spirledaxis/LNMQ-Alarm-Clock/main/IMG_9301.JPEG

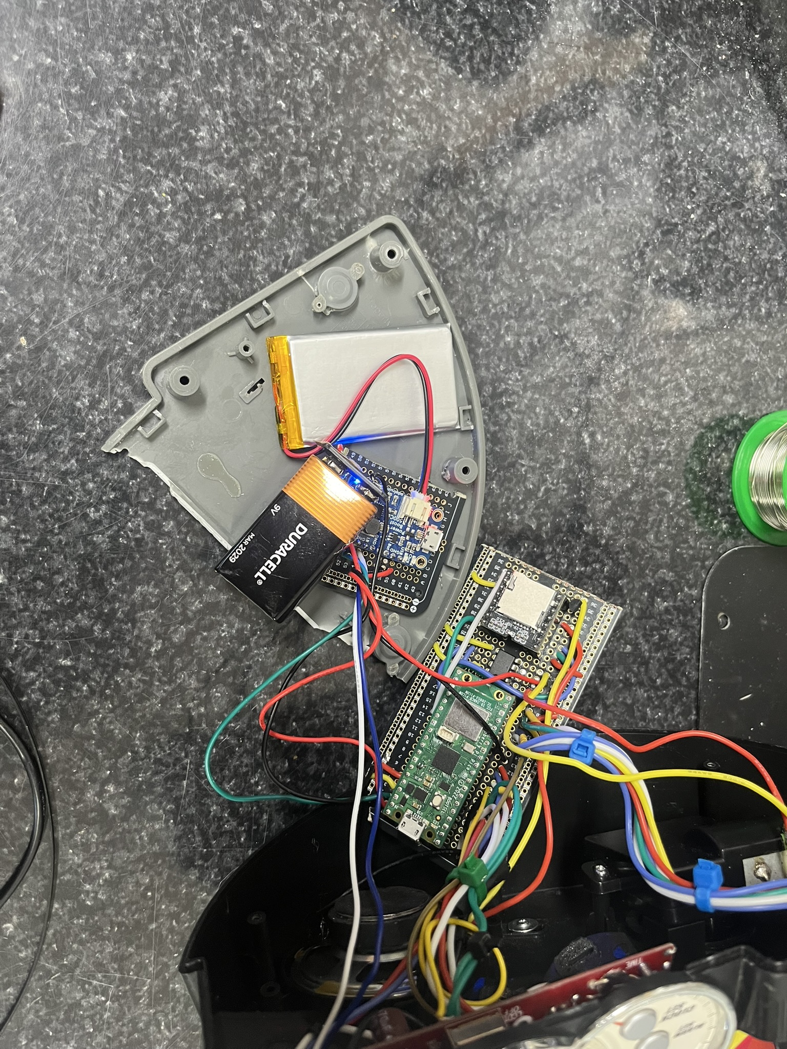
main/IMG_9301.JPEG
