spirledaxis/LNMQ-Alarm-Clock/main/IMG_9304.JPEG

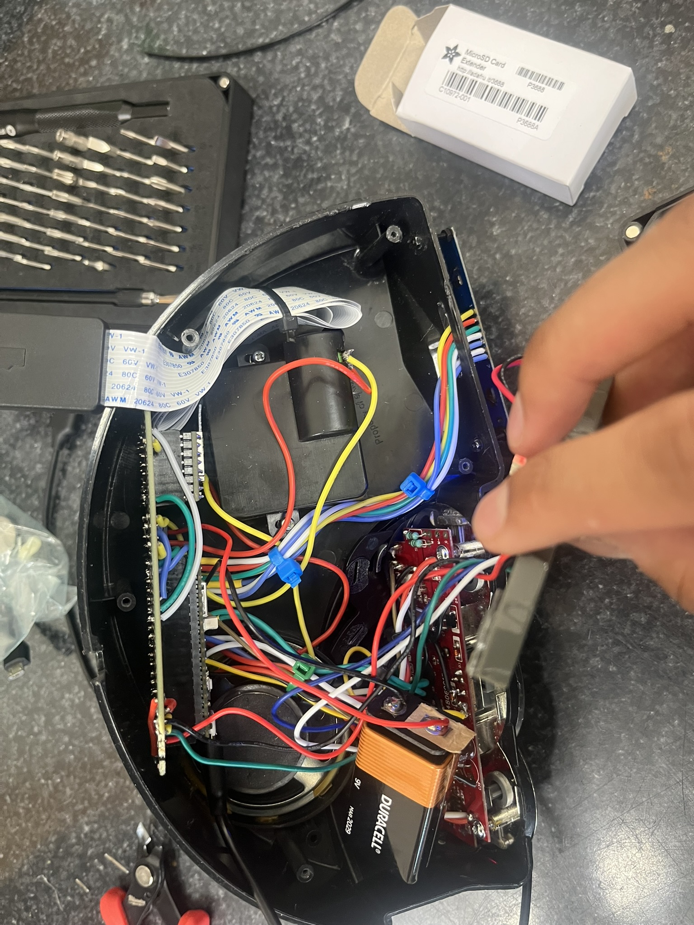
main/IMG_9304.JPEG
