spirledaxis/LNMQ-Alarm-Clock/main/IMG_9452.jpg

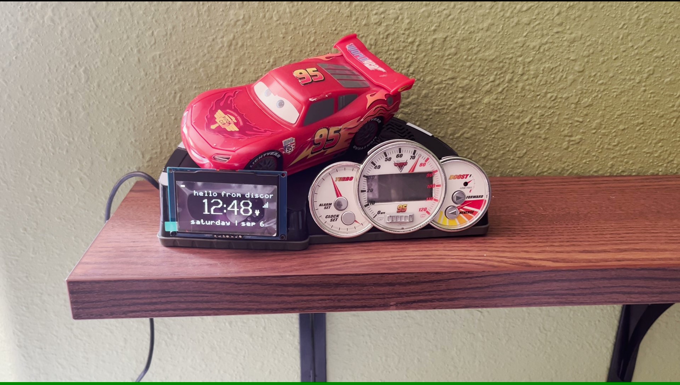
main/IMG_9452.jpg
