spirledaxis/LNMQ-Alarm-Clock/hardware/motor_movements.py

i_am_speed = [
    ('w', 600, 100),
    ('r', 1133, 30),  # exhale
    ('l', 733, 40),  # exhale 2
    ('w', 6300, 100),
    ('r', 2184, 100),  # racing sounds
    ('l', 1133, 80),  # one winner
    ('r', 1183, 80),  # 42 losers
    ('w', 2634, 100),  # I eat losers for breakfeast
    ('r', 2633, 100),  # racing sounds
    ('w', 813, 100),  # "speed"
    ('r', 2500, 100),  # racing sounds
    ('l', 884, 80),  # I am faster than fast
    ('r', 1150, 80),  # quicker than quick
    ('w', 1433, 100),  # I am lightning
]

freedom_dive = [
    ('l', 333.0, 100),
    ('r', 833.0, 100),
    ('l', 867.0, 100),
    ('r', 1017.0, 100),
    ('l', 1100.0, 100),
    ('r', 1100.0, 100),
    ('l', 1050.0, 100),
    ('r', 1066.0, 100),
    ('l', 567.0, 100),
    ('r', 567.0, 100),
    ('l', 1250.0, 100),
    ('r', 1066.0, 100),
    ('l', 417.0, 100),
    ('r', 583.0, 100),
    ('l', 1150.0, 100),
    ('r', 467.0, 100),
    ('l', 550.0, 100),
    ('r', 1150.001, 100),
    ('l', 516.999, 100),
    ('r', 500.0, 100),
    ('l', 1066.0, 100),
    ('r', 1084.0, 100),
    ('l', 1100.0, 100),
    ('r', 466.0, 100),
    ('l', 584.002, 100),
    ('r', 532.999, 100),
    ('l', 533.001, 100),
    ('r', 517.0, 100),
    ('l', 566.999, 100),
    ('r', 1132.999, 100),
    ('l', 1050.001, 100),
    ('r', 632.999, 100),
    ('l', 517.0, 100),
    ('r', 299.999, 100),
    ('l', 283.001, 100),
    ('r', 250.0, 100),
    ('l', 233.999, 100),
    ('r', 1083.0, 100),
    ('l', 483.0, 100),
    ('r', 584.0, 100),
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
]

default = [
    ('r', 400, 100),  # quick burst right at full speed
    ('l', 400, 100),  # quick burst left at full speed
    ('r', 300, 100),  # shorter burst right
    ('l', 300, 100),  # shorter burst left
    ('w', 200, 0),    # brief pause
    ('r', 600, 80),   # longer slide right at slightly lower speed
    ('l', 600, 80),   # longer slide left
    ('w', 100, 0),    # quick pause
    ('r', 200, 100),  # quick snap right
    ('l', 200, 100),  # quick snap left
    ('w', 300, 0),    # pause before finish
    ('r', 500, 90),   # final strong move right
    ('l', 500, 90)    # final strong move left
]

eta = [
    ('w', 125, 100),
    ('r', 416, 100),
    ('l', 334, 100),
    ('r', 291, 100),
    ('l', 125, 100),
    ('r', 207, 100),
    ('l', 210, 100),
    ('r', 292, 100),
    ('l', 250, 100),
    ('r', 375, 100),
    ('l', 375, 100),
    ('r', 333, 100),
    ('l', 83.0, 100),
    ('r', 167, 100),
    ('l', 208, 100),
    ('r', 500, 100),
    ('l', 417, 100),
    ('r', 375, 100),
    ('l', 292, 100),
    ('r', 125, 100),
    ('l', 125, 100),
    ('r', 291, 100),
    ('l', 209, 100),
    ('r', 291, 100),
    ('l', 375, 100),
    ('r', 417, 100),
    ('l', 292, 100),
    ('r', 125, 100),
    ('l', 500, 100),
    ('r', 291, 100),
    ('l', 125, 100),
    ('r', 209, 100),
    ('l', 16000, 60)
]

stay_with_me = [
    ("w", 5416, 100),
    ("r", 125, 100),
    ("l", 417, 100),
    ("r", 125, 100),
    ("l", 1292, 100),
    ("r", 2333, 100),
    ("l", 1083, 100),
    ("r", 1042, 100),
    ("l", 2292, 100),
    ("r", 1166, 100),
    ("l", 1042, 100),
    ("r", 4458, 100),
    ("l", 250, 100),
    ("r", 292, 100),
    ("l", 250, 100),
    ("r", 1417, 100),
    ("l", 250, 100),
    ("r", 291, 100),
    ("l", 250, 100),
    ("r", 1334, 100),
    ("l", 2250, 100),
    ("r", 1125, 100),
    ("l", 1041, 100),
]

clash_royale = [
    ("w", 2666, 100),
    ("r", 1834, 100),
    ("l", 458, 100),
    ("r", 500, 100),
    ("w", 3250, 100),
    ("r", 458, 100),
    ("w", 459, 100),
    ("r", 1666, 100),
    ("l", 417, 100),
    ("r", 917, 100),
    ("l", 1250, 100),
    ("r", 1041, 100),
    ("l", 459, 100),
    ("r", 500, 100),
    ("l", 1583, 100),
    ("w", 1042, 100),
    ("l", 1000, 100),
    ("r", 1791, 100),
    ("l", 334, 100),
    ("r", 416, 100),
    ("l", 917, 100),
    ("w", 2083, 100),
    ("l", 417, 100),
    ("r", 1333, 100),
    ("l", 375, 100),
    ("r", 875, 100)
]
