spirledaxis/LNMQ-Alarm-Clock/bigicons.py

booticon = bytearray([
    0x00, 0x00, 0x00, 0x00, 0x00, 0x00, 0x00, 0x00, 0x00, 0x00, 0x00, 0x00, 0x00, 0x00, 0x00, 0x00,
    0x00, 0x00, 0x00, 0x00, 0x00, 0x00, 0x00, 0x00, 0x00, 0x80, 0x80, 0xc0, 0xc0, 0x40, 0xc0, 0xc0,
    0x80, 0x80, 0x00, 0x00, 0x00, 0x00, 0x00, 0x00, 0x00, 0x00, 0x00, 0x00, 0x00, 0x00, 0x00, 0x00,
    0x00, 0x00, 0x00, 0x00, 0x00, 0x00, 0x00, 0x00, 0x00, 0x00, 0x00, 0x00, 0x00, 0x00, 0x00, 0x00,
    0x00, 0x00, 0x00, 0x00, 0x00, 0x00, 0x00, 0x00, 0x00, 0x00, 0x00, 0x00, 0x00, 0x00, 0x00, 0x00,
    0x00, 0x00, 0x00, 0x00, 0x00, 0x00, 0x00, 0x00, 0x00, 0x00, 0x00, 0x00, 0x00, 0x80, 0x80, 0xc0,
    0xc0, 0x40, 0xc0, 0xc0, 0x80, 0x80, 0x00, 0x00, 0x00, 0x00, 0x00, 0x00, 0x00, 0x00, 0x00, 0x00,
    0x00, 0x00, 0x00, 0x00, 0x00, 0x00, 0x00, 0x00, 0x00, 0x00, 0x00, 0x00, 0x00, 0x00, 0x00, 0x00,
    0x00, 0x00, 0x00, 0x00, 0x00, 0x00, 0x00, 0x00, 0x00, 0x00, 0x00, 0x00, 0x00, 0x00, 0x00, 0x00,
    0x00, 0x00, 0x00, 0x80, 0xe0, 0xfc, 0x7e, 0x7e, 0x7b, 0x77, 0x6f, 0x5f, 0x3f, 0x80, 0x3f, 0x5f,
    0x6f, 0x77, 0x7b, 0x7f, 0x7e, 0xfc, 0xe0, 0x60, 0x60, 0x60, 0x60, 0x60, 0x00, 0x00, 0x00, 0xfe,
    0xfe, 0x00, 0x00, 0x00, 0x00, 0xe0, 0xf8, 0x1e, 0x06, 0x06, 0x1e, 0xf8, 0xe0, 0x00, 0x00, 0xe0,
    0xf8, 0x1e, 0x06, 0x06, 0x1e, 0xf8, 0xe0, 0x00, 0x00, 0xf8, 0xfe, 0x06, 0x06, 0x06, 0xfe, 0xfe,
    0x00, 0x00, 0x00, 0x60, 0x60, 0x60, 0x60, 0x60, 0xf8, 0x7c, 0x7e, 0x7e, 0x7b, 0x77, 0x6f, 0x5f,
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
    0x00, 0x00, 0x00, 0x00, 0x00, 0x00, 0x00, 0x00, 0x00, 0x00, 0x00, 0x00, 0x80, 0x80, 0x80, 0x80, 
    0xe0, 0x60, 0x60, 0x78, 0x18, 0x18, 0x18, 0x1e, 0x1e, 0x06, 0x06, 0x07, 0x00, 0x00, 0x00, 0x00, 
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
