spirledaxis/LNMQ-Alarm-Clock/displaystates/fonts.py

from lib import XglcdFont

print("loading fonts...")
timefont = XglcdFont('displaystates/Proxy24x31.bin', 24, 31)
bally = XglcdFont('displaystates/Bally7x9.bin', 7, 9)
bally_mini = XglcdFont('displaystates/Bally5x8.bin', 5, 8)
