spirledaxis/LNMQ-Alarm-Clock/main/tempuratures.py

from machine import ADC, I2C, Pin  # type: ignore

import config

# straight from Mr.GPT, idk how accurate it is
# TODO: look at adafruits circutpython and mirror it in micro

# TMP117 default I2C address
TMP117_ADDR = 0x48
TMP117_TEMP_REG = 0x00

# Initialize I2C (adjust pins and bus as needed)
i2c = I2C(1, scl=Pin(config.tmp_scl), sda=Pin(config.tmp_sda), freq=400000)


def get_ambient_temp():
    # Read 2 bytes from temperature register
    data = i2c.readfrom_mem(TMP117_ADDR, TMP117_TEMP_REG, 2)

    # Combine high and low bytes
    raw_temp = (data[0] << 8) | data[1]

    # Handle negative temperatures (2's complement, 16-bit)
    if raw_temp & 0x8000:
        raw_temp -= 1 << 16

    # Each LSB = 7.8125e-3 °C
    temp_c = raw_temp * 0.0078125
    f = (temp_c * 9 / 5) + 32
    return f


def get_internal_temp():
    sensor_temp = ADC(4)
    conversion_factor = 3.3 / 65535  # 16-bit ADC scaling

    reading = sensor_temp.read_u16() * conversion_factor
    temperature = 27 - (reading - 0.706) / 0.001721
    return temperature
